PJ-Verweij/LowCostHighPrecisionPositioning-GNSSreferencestation/CAD_model/Solarpanel/Solarpanel.Victron_20watt.Assembly.SLDASM

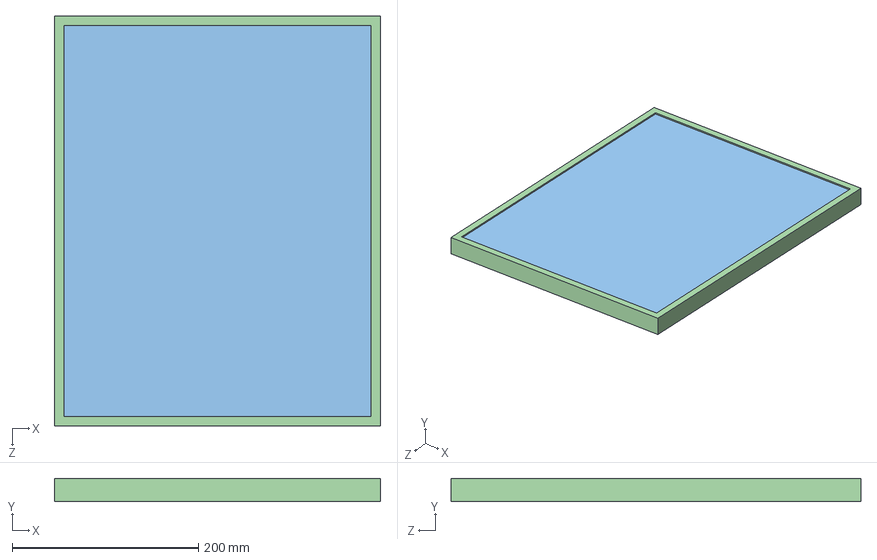
[picture p9: CAD file, 2021-05-01]
CAD_model/Solarpanel/Solarpanel.Victron_20watt.Assembly.SLDASM
350.0 x 25.0 x 440.0 mm
Solarpanel.sides
Solarpanel.glass
Solarpanel.cells
Solarpanel.backplate
