PJ-Verweij/LowCostHighPrecisionPositioning-GNSSreferencestation/CAD_model/Main_unit/PCB-components/Main-Unit.SIM800_GPRSmodem_Withheader.Assembly.SLDASM

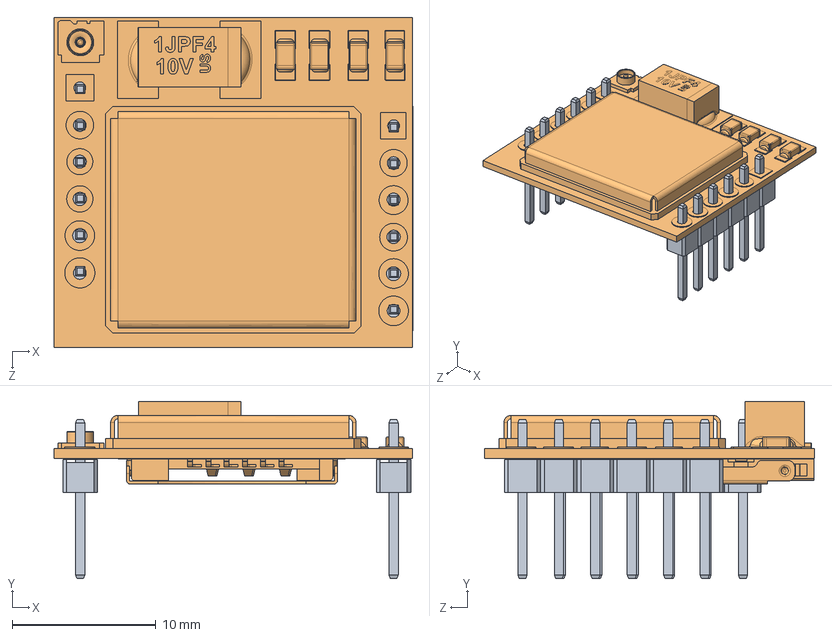
[picture p16: CAD file, 2021-05-01]
CAD_model/Main_unit/PCB-components/Main-Unit.SIM800_GPRSmodem_Withheader.Assembly.SLDASM
25.0 x 12.4 x 23.0 mm
Main-Unit.SIM800_GPRSmodem
Main-Unit.Male_Pin_2.54_mm x 12
