PJ-Verweij/LowCostHighPrecisionPositioning-GNSSreferencestation/CAD_model/Main_unit/Enclosure-components/Main-Unit.Enclosure.Box.SLDPRT

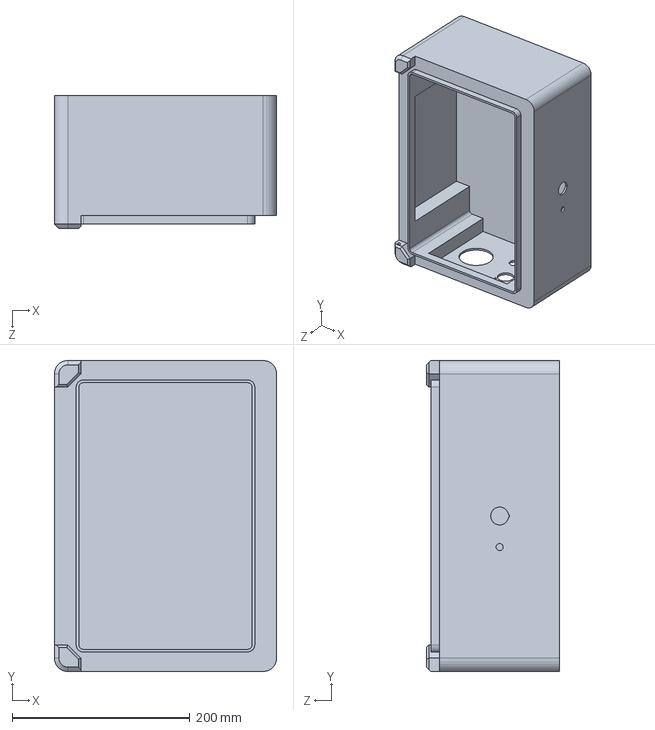
[picture p18: CAD file, 2021-05-01]
CAD_model/Main_unit/Enclosure-components/Main-Unit.Enclosure.Box.SLDPRT
250.0 x 350.0 x 150.0 mm
