PJ-Verweij/LowCostHighPrecisionPositioning-GNSSreferencestation/CAD_model/Main_unit/PCB-components/Main-Unit.Raspberry_PI_Zero.Assembly.SLDASM

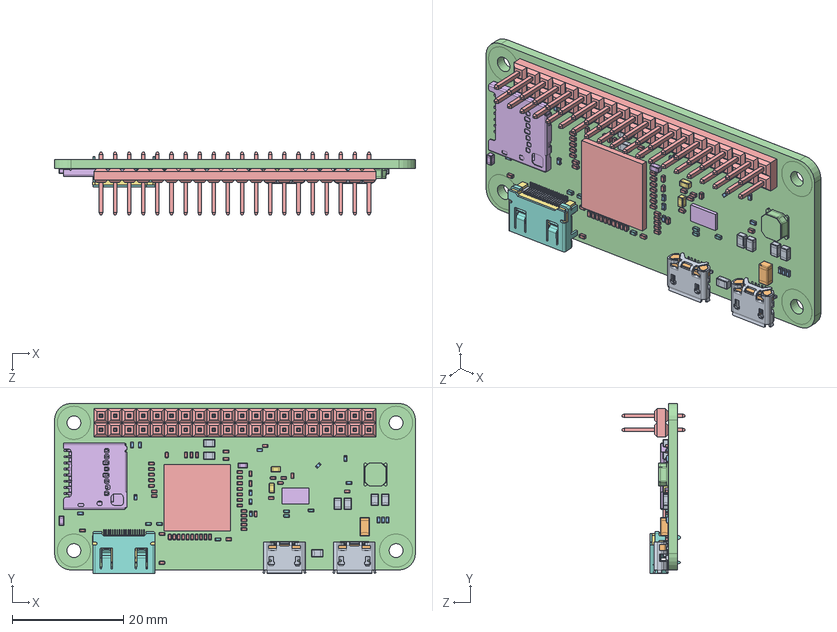
[picture p19: CAD file, 2021-05-01]
CAD_model/Main_unit/PCB-components/Main-Unit.Raspberry_PI_Zero.Assembly.SLDASM
65.0 x 30.6 x 11.4 mm
shield.step x 2
socket_housing.step x 2
socket_plate.step x 2
terminal.step x 10
CAPC-0402-T0.55-BN.step x 49
CAPC-0603-T0.9-BN.step x 2
INDC-0603.step x 2
INDC-0402.step x 6
CAPC-0805-T0.95-BN.step x 7
CAPC-1206-T1.4-BN.step
RESC-0402.step x 14
SRN4018.step
Components-0.step
Components-1.step
Housing.step
Shielding.step
Housing2.step
Pin1.step x 18
Pin2.step
Board.step
HDRV40W64P254_2X20_5080X508X838B.step
Micro SD slot.step
