PJ-Verweij/LowCostHighPrecisionPositioning-GNSSreferencestation/CAD_model/Main_unit/PCB-components/Pinheaders/Main-Unit.8x_Pinheader_2.54mm.Assembly.SLDASM

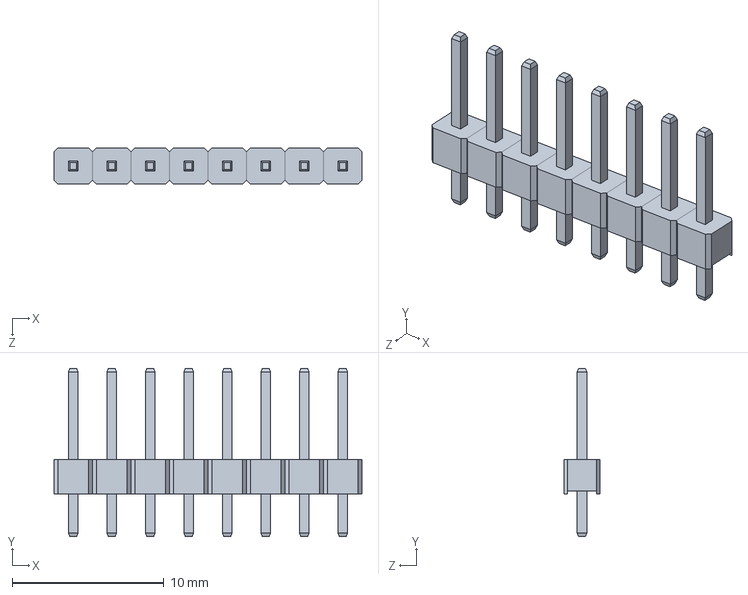
[picture p20: CAD file, 2021-05-01]
CAD_model/Main_unit/PCB-components/Pinheaders/Main-Unit.8x_Pinheader_2.54mm.Assembly.SLDASM
20.3 x 11.1 x 2.40 mm
Main-Unit.Male_Pin_2.54_mm x 8
