PJ-Verweij/LowCostHighPrecisionPositioning-GNSSreferencestation/CAD_model/Main_unit/Cable-gland-pg7-pg19/Main-Unit.Cable_Gland_PG9.Assembly.SLDASM

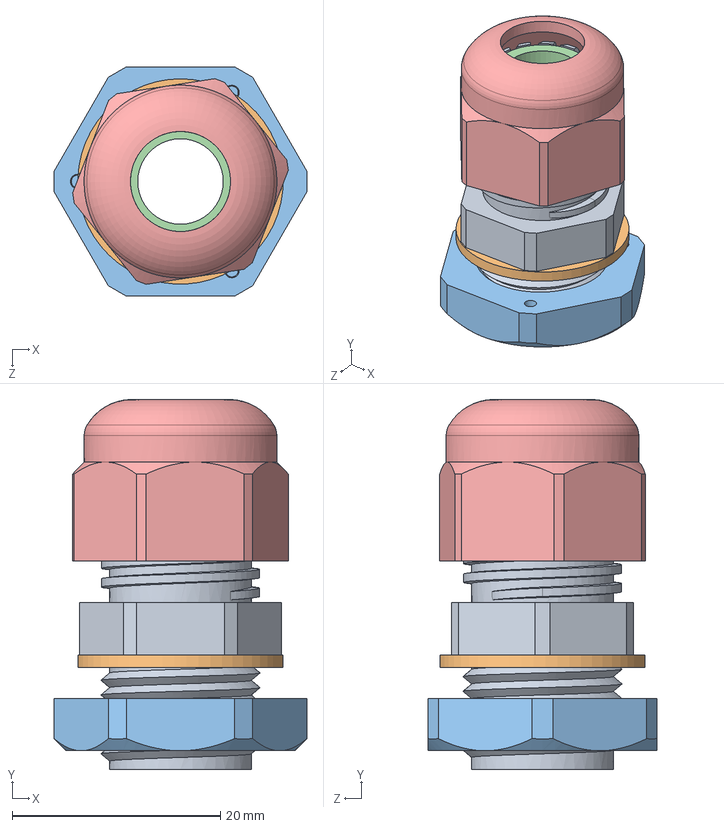
[picture p21: CAD file, 2021-05-01]
CAD_model/Main_unit/Cable-gland-pg7-pg19/Main-Unit.Cable_Gland_PG9.Assembly.SLDASM
24.2 x 35.5 x 22.0 mm
Cable Gland PG7-PG19 Body
Cable Gland PG7-PG19 Washer
Cable Gland PG7-PG19 Lock Nut
Cable Gland PG7-PG19 Sleeve
Cable Gland PG7-PG19 Gland Nut
