PJ-Verweij/LowCostHighPrecisionPositioning-GNSSreferencestation/CAD_model/Main_unit/Enclosure-components/Main-Unit.Case_LED_CML_19010051.SLDPRT

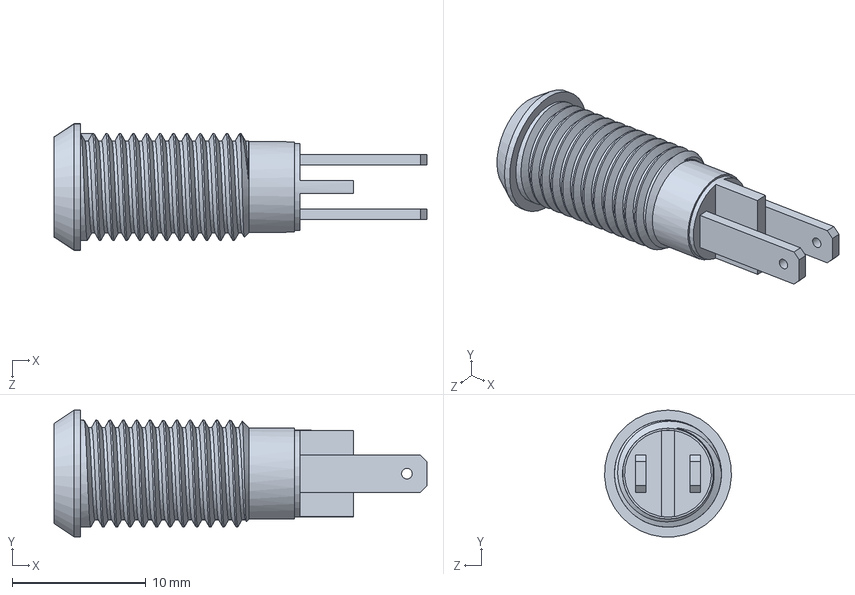
[picture p22: CAD file, 2021-05-01]
CAD_model/Main_unit/Enclosure-components/Main-Unit.Case_LED_CML_19010051.SLDPRT
27.9 x 9.48 x 9.49 mm
