PJ-Verweij/LowCostHighPrecisionPositioning-GNSSreferencestation/CAD_model/Main_unit/Enclosure-components/Main-Unit.Enclosure.Rubber.SLDPRT

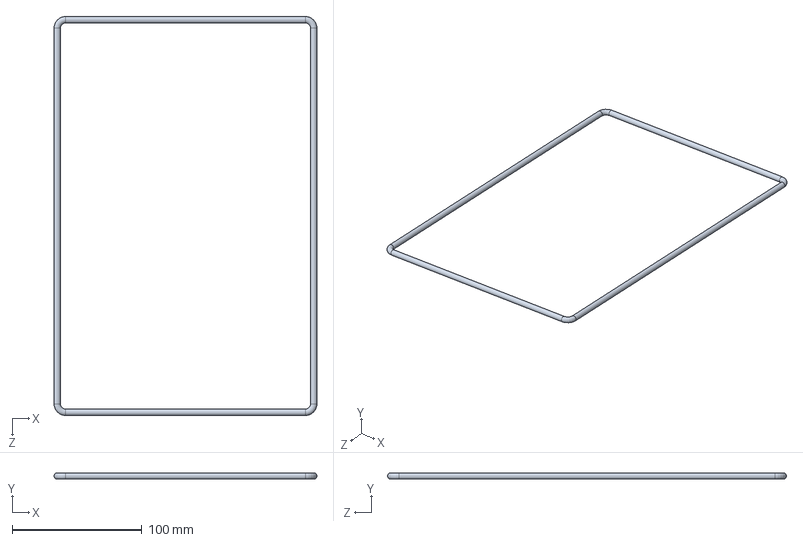
[picture p23: CAD file, 2021-05-01]
CAD_model/Main_unit/Enclosure-components/Main-Unit.Enclosure.Rubber.SLDPRT
203.0 x 5.00 x 308.0 mm
