PJ-Verweij/LowCostHighPrecisionPositioning-GNSSreferencestation/CAD_model/Main_unit/PCB-components/Main-Unit.M4_Insulated_crimp_ring.SLDPRT

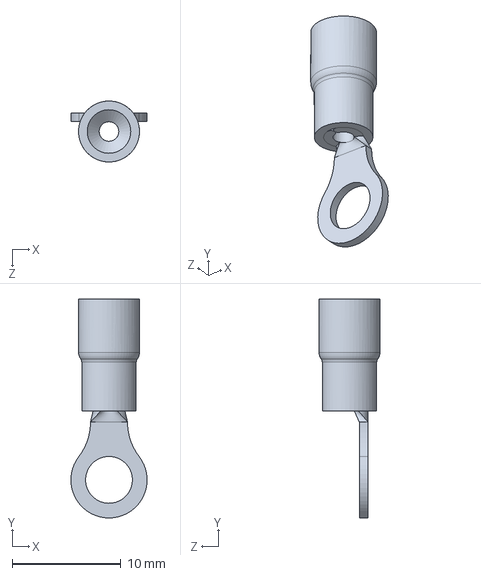
[picture p24: CAD file, 2021-05-01]
CAD_model/Main_unit/PCB-components/Main-Unit.M4_Insulated_crimp_ring.SLDPRT
7.00 x 20.1 x 5.60 mm
