PJ-Verweij/LowCostHighPrecisionPositioning-GNSSreferencestation/CAD_model/Antenna/Antenna.Antennatop.Assembly.SLDASM

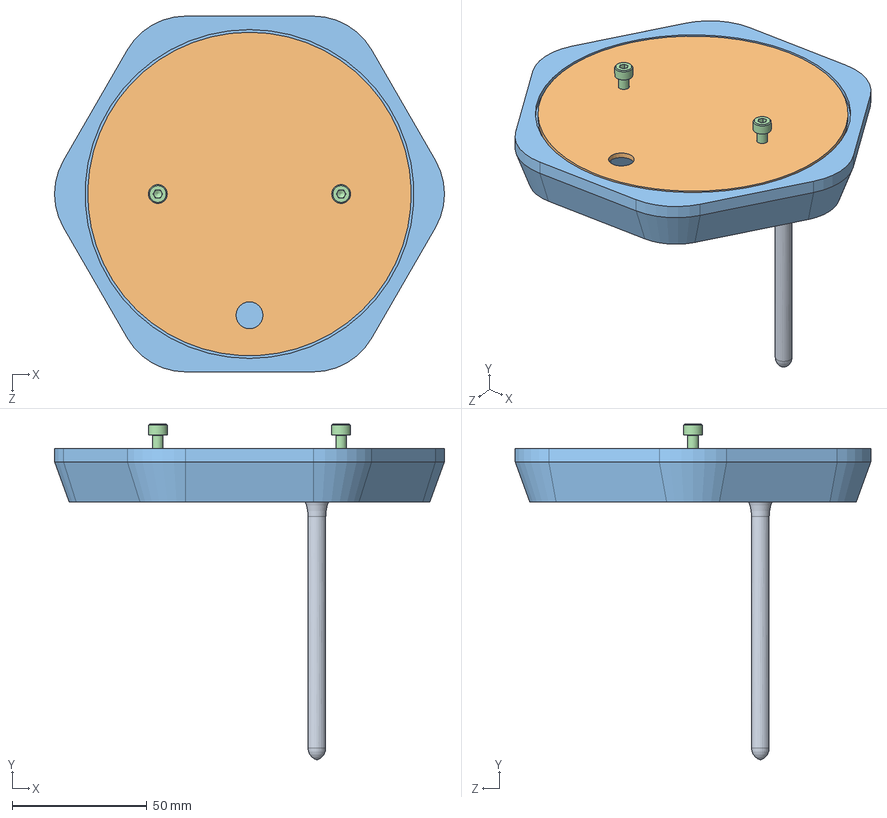
[picture p25: CAD file, 2021-05-01]
CAD_model/Antenna/Antenna.Antennatop.Assembly.SLDASM
144.7 x 124.6 x 132.0 mm
Antennatop.Base
Antennatop.Groundplane
Antennatop.Cellular-Antenna
socket head cap screw_am x 3
hex nut style 1_am x 2
