PJ-Verweij/LowCostHighPrecisionPositioning-GNSSreferencestation/CAD_model/Main_unit/PCB-components/Main-Unit.M2.5x10_hexagonal_spacer.SLDPRT

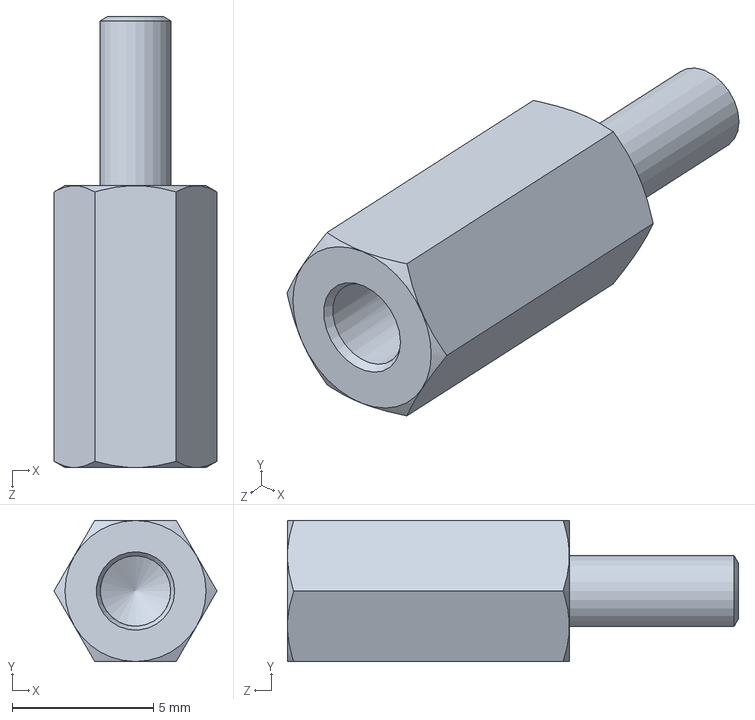
[picture p26: CAD file, 2021-05-01]
CAD_model/Main_unit/PCB-components/Main-Unit.M2.5x10_hexagonal_spacer.SLDPRT
5.78 x 5.01 x 16.0 mm
