PJ-Verweij/LowCostHighPrecisionPositioning-GNSSreferencestation/CAD_model/Main_unit/PCB-components/Main-Unit.SMA_Male_connector.SLDPRT

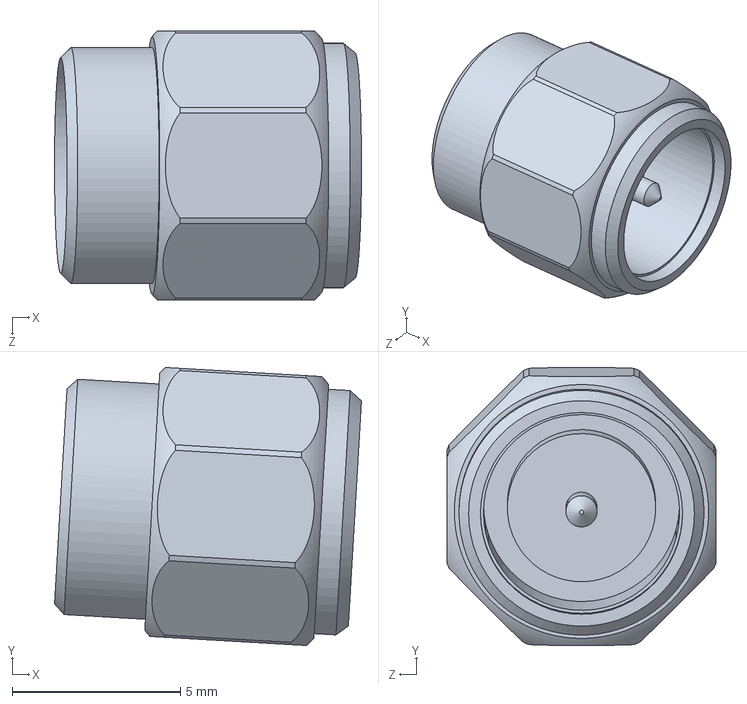
[picture p27: CAD file, 2021-05-01]
CAD_model/Main_unit/PCB-components/Main-Unit.SMA_Male_connector.SLDPRT
9.12 x 8.26 x 8.00 mm
