PJ-Verweij/LowCostHighPrecisionPositioning-GNSSreferencestation/CAD_model/Main_unit/Enclosure-components/Main-Unit.M4x10_Hexagonal_Spacer.SLDPRT

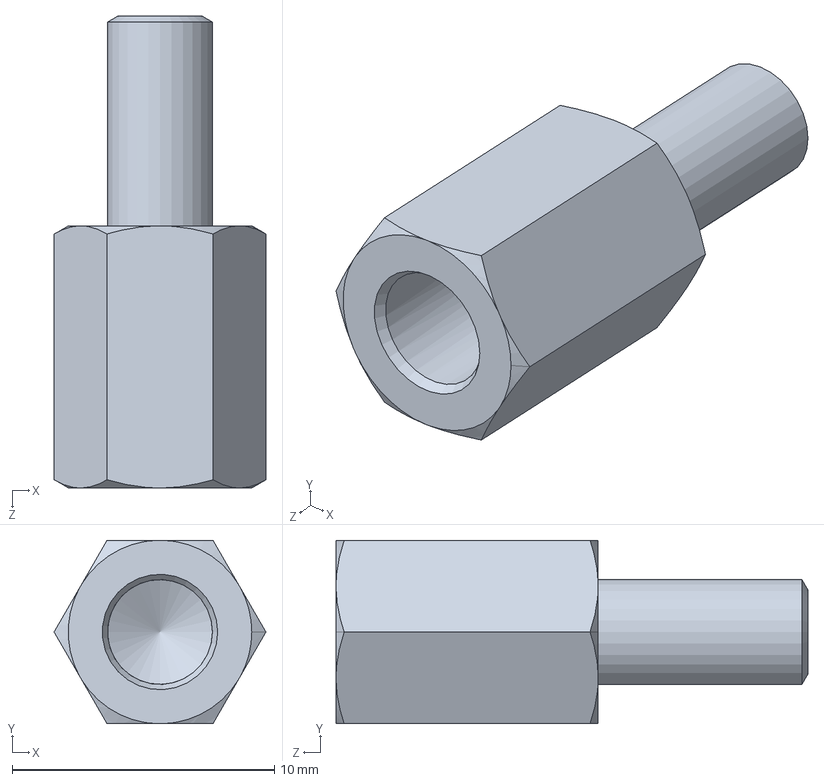
[picture p28: CAD file, 2021-05-01]
CAD_model/Main_unit/Enclosure-components/Main-Unit.M4x10_Hexagonal_Spacer.SLDPRT
8.08 x 7.00 x 18.0 mm
