PJ-Verweij/LowCostHighPrecisionPositioning-GNSSreferencestation/CAD_model/Main_unit/PCB-components/Main-Unit.5x20_Fuse.SLDPRT

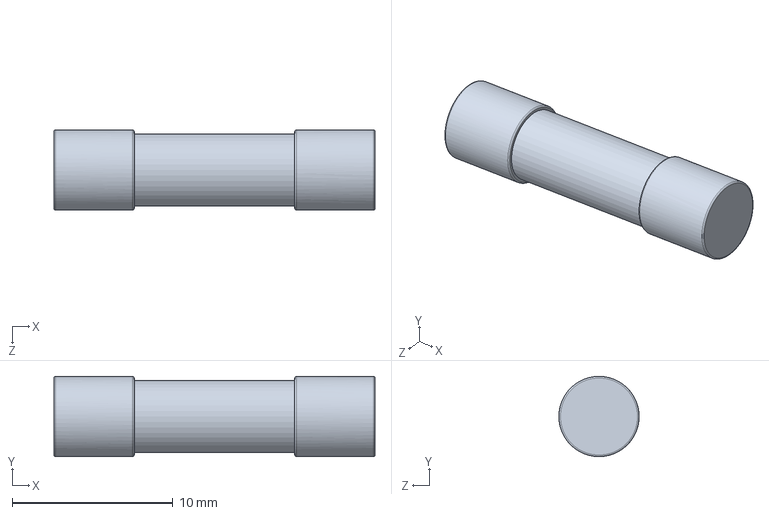
[picture p29: CAD file, 2021-05-01]
CAD_model/Main_unit/PCB-components/Main-Unit.5x20_Fuse.SLDPRT
20.0 x 5.00 x 5.00 mm
