PJ-Verweij/LowCostHighPrecisionPositioning-GNSSreferencestation/CAD_model/Antenna/Antennatop.Cellular-Antenna.SLDPRT

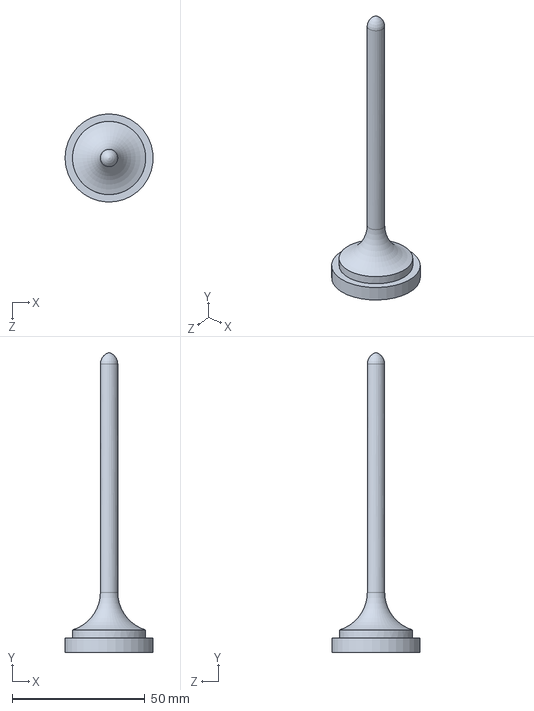
[picture p30: CAD file, 2021-05-01]
CAD_model/Antenna/Antennatop.Cellular-Antenna.SLDPRT
33.1 x 113.0 x 33.2 mm
