PJ-Verweij/LowCostHighPrecisionPositioning-GNSSreferencestation/CAD_model/Solarpanel/frame.SLDPRT

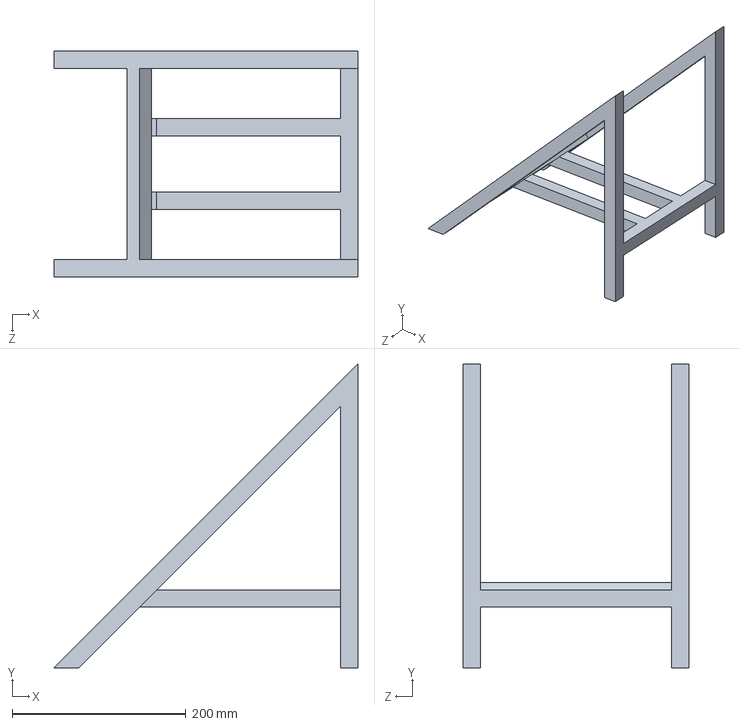
[picture p31: CAD file, 2021-05-01]
CAD_model/Solarpanel/frame.SLDPRT
350.0 x 350.0 x 260.0 mm
