PJ-Verweij/LowCostHighPrecisionPositioning-GNSSreferencestation/Productionfiles/Antennatop.Base-hole25,5mm.STL

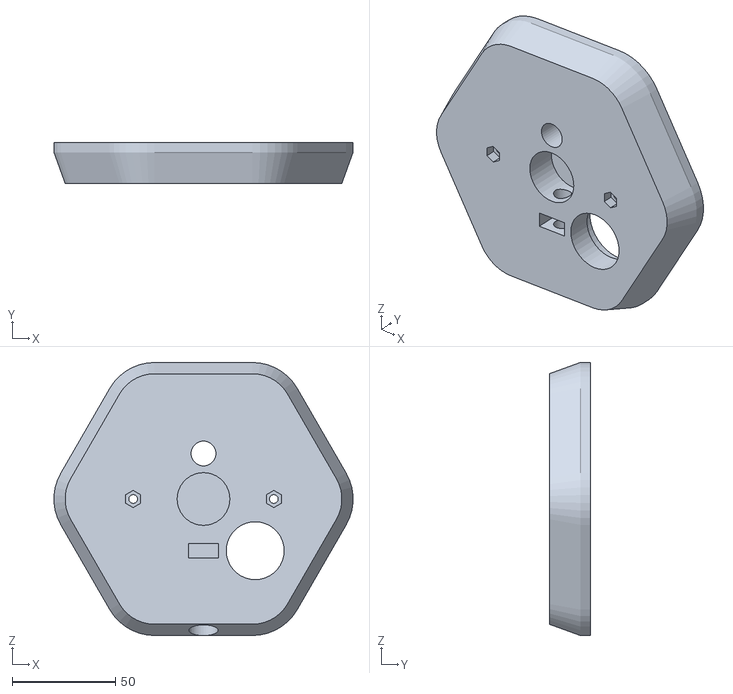
[picture p32: CAD file, 2021-05-01]
Productionfiles/Antennatop.Base-hole25,5mm.STL
144.5 x 20.0 x 132.0
