PJ-Verweij/LowCostHighPrecisionPositioning-GNSSreferencestation/CAD_model/Main_unit/Cable-gland-pg7-pg19/Cable Gland PG7-PG19 Sleeve.SLDPRT

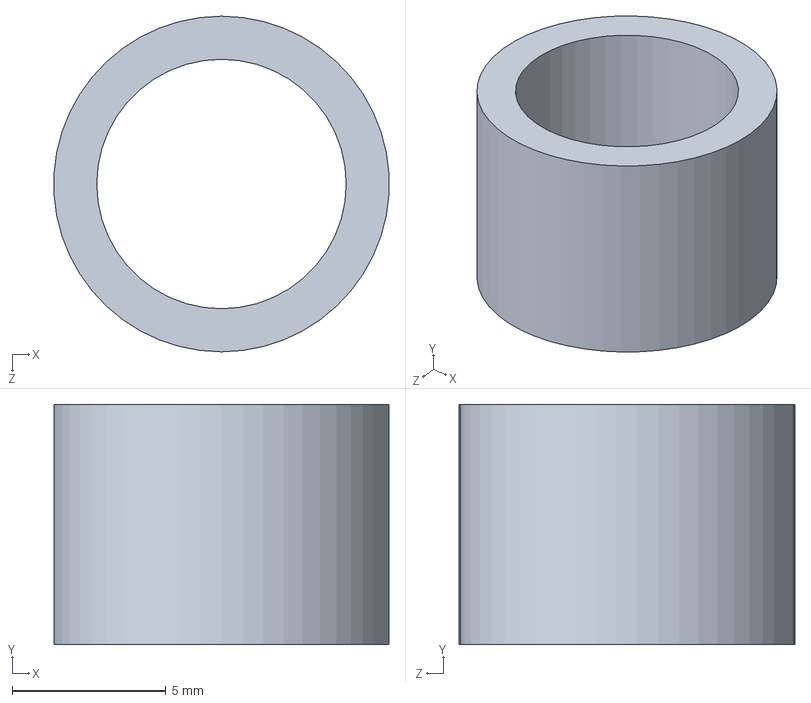
[picture p33: CAD file, 2021-05-01]
CAD_model/Main_unit/Cable-gland-pg7-pg19/Cable Gland PG7-PG19 Sleeve.SLDPRT
10.9 x 7.80 x 10.9 mm
