PJ-Verweij/LowCostHighPrecisionPositioning-GNSSreferencestation/CAD_model/Antenna/Antenna.Pole-1000mmx25mm.SLDPRT

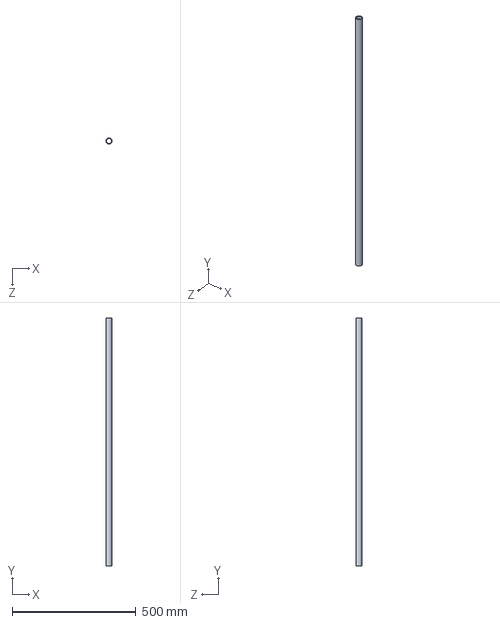
[picture p34: CAD file, 2021-05-01]
CAD_model/Antenna/Antenna.Pole-1000mmx25mm.SLDPRT
25.0 x 1000.0 x 25.0 mm
