PJ-Verweij/LowCostHighPrecisionPositioning-GNSSreferencestation/CAD_model/Main_unit/Toolbox-components/cross ph tapping 968_din.sldprt

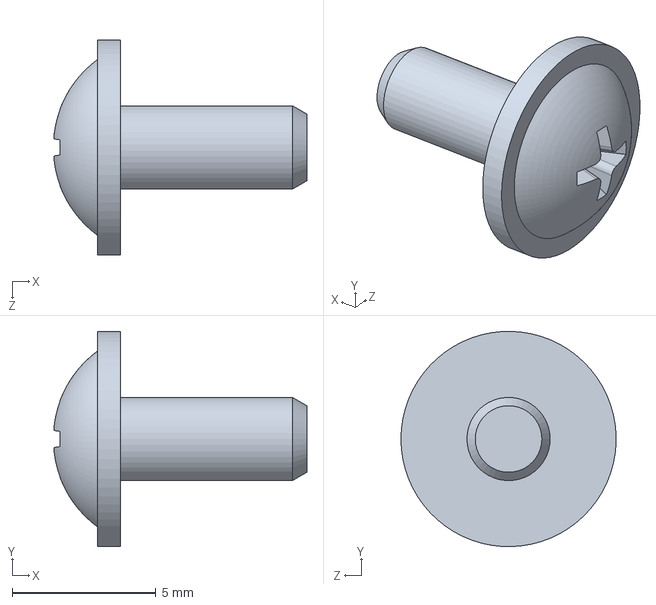
[picture p35: CAD file, 2021-05-01]
CAD_model/Main_unit/Toolbox-components/cross ph tapping 968_din.sldprt
8.81 x 7.50 x 7.50 mm
