PJ-Verweij/LowCostHighPrecisionPositioning-GNSSreferencestation/CAD_model/Solarpanel/Solarpanel.glass.SLDPRT

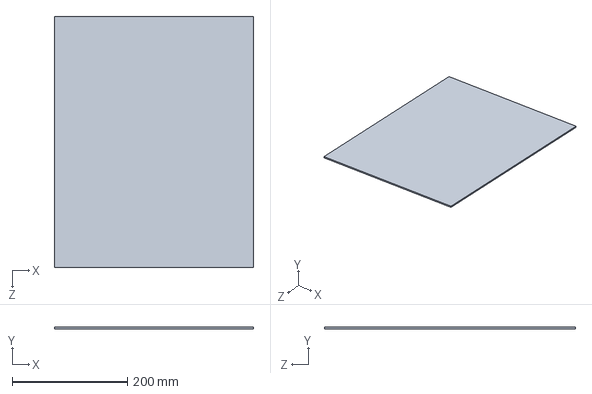
[picture p36: CAD file, 2021-05-01]
CAD_model/Solarpanel/Solarpanel.glass.SLDPRT
346.0 x 3.00 x 436.0 mm
