PJ-Verweij/LowCostHighPrecisionPositioning-GNSSreferencestation/CAD_model/Antenna/thread adapter antenna top.SLDPRT

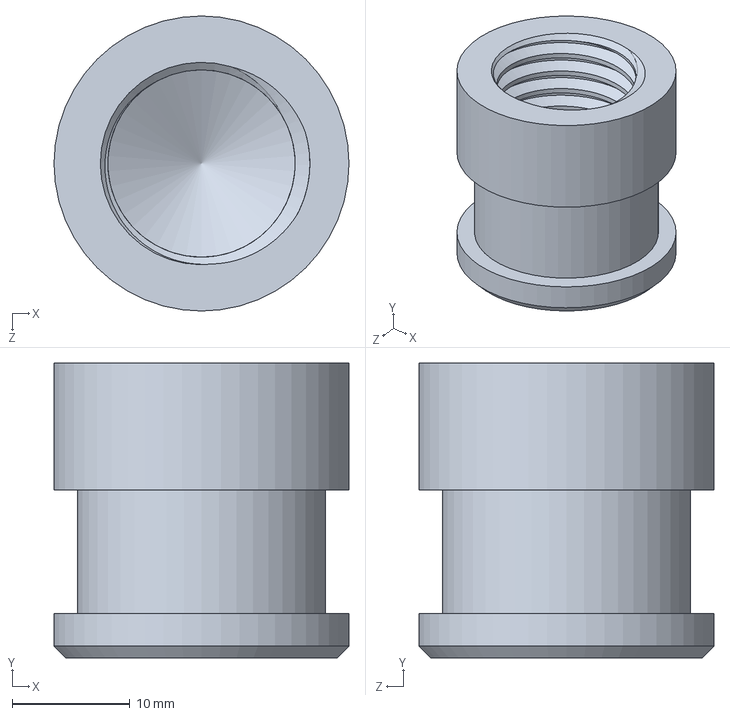
[picture p37: CAD file, 2021-05-01]
CAD_model/Antenna/thread adapter antenna top.SLDPRT
25.0 x 25.0 x 25.0 mm
