PJ-Verweij/LowCostHighPrecisionPositioning-GNSSreferencestation/CAD_model/Main_unit/Cable-gland-pg7-pg19/Cable Gland PG7-PG19 Body.SLDPRT

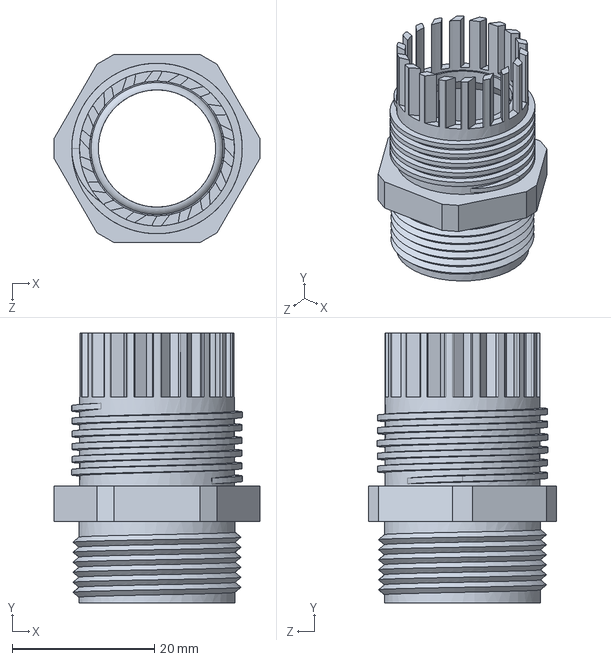
[picture p38: CAD file, 2021-05-01]
CAD_model/Main_unit/Cable-gland-pg7-pg19/Cable Gland PG7-PG19 Body.SLDPRT
29.0 x 38.0 x 26.5 mm
