PJ-Verweij/LowCostHighPrecisionPositioning-GNSSreferencestation/CAD_model/Solarpanel/Solarpanel.sides.SLDPRT

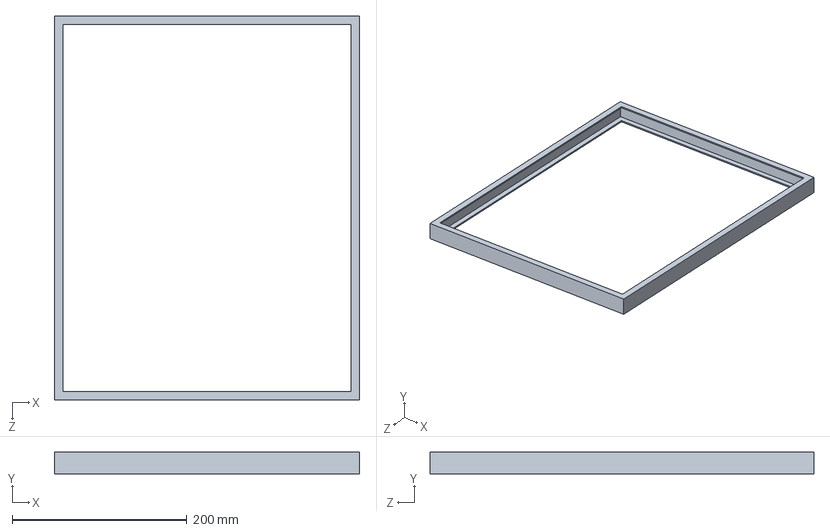
[picture p39: CAD file, 2021-05-01]
CAD_model/Solarpanel/Solarpanel.sides.SLDPRT
350.0 x 25.0 x 440.0 mm
