PJ-Verweij/LowCostHighPrecisionPositioning-GNSSreferencestation/CAD_model/Antenna/Antennatop.Groundplane.SLDPRT

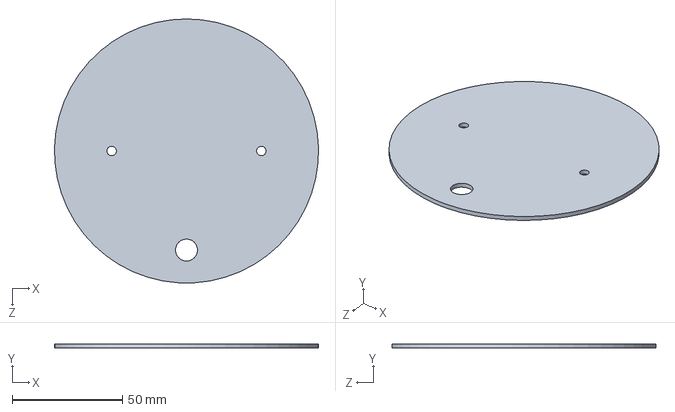
[picture p40: CAD file, 2021-05-01]
CAD_model/Antenna/Antennatop.Groundplane.SLDPRT
119.9 x 2.00 x 120.0 mm
