PJ-Verweij/LowCostHighPrecisionPositioning-GNSSreferencestation/CAD_model/Solarpanel/Solarpanel.cells.SLDPRT

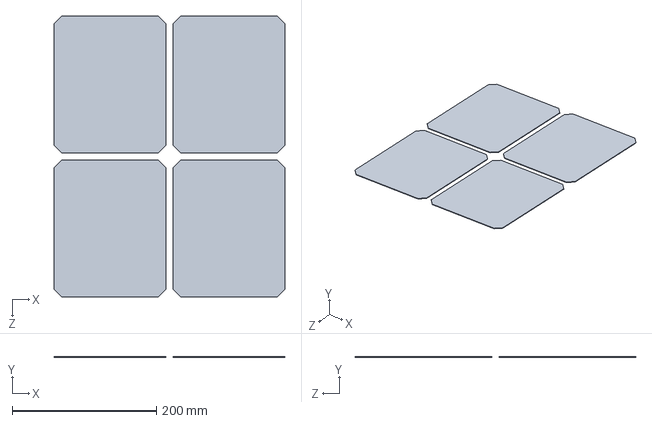
[picture p41: CAD file, 2021-05-01]
CAD_model/Solarpanel/Solarpanel.cells.SLDPRT
320.0 x 1.00 x 390.0 mm
