PJ-Verweij/LowCostHighPrecisionPositioning-GNSSreferencestation/CAD_model/Solarpanel/Solarpanel.Example-bracket.SLDPRT

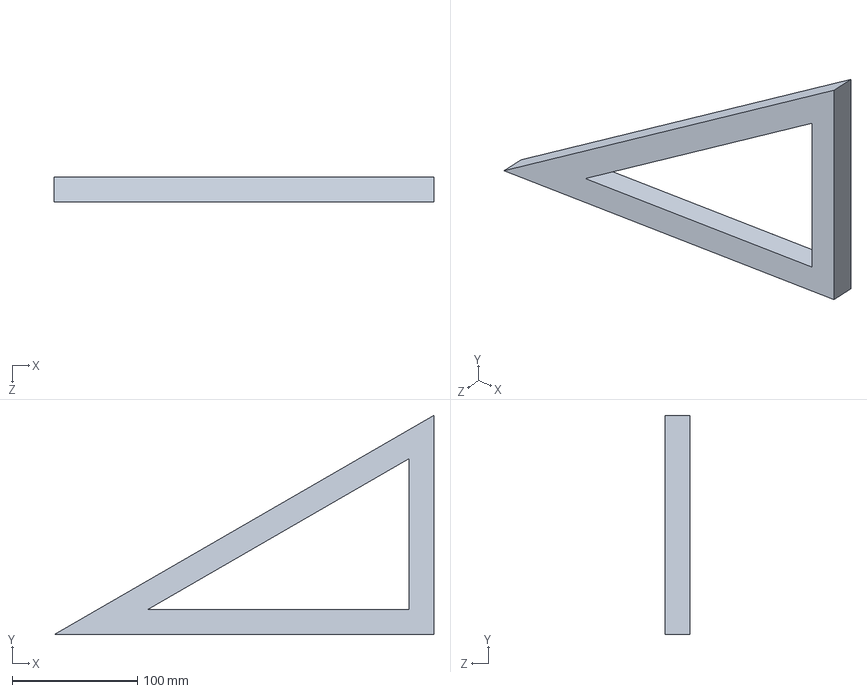
[picture p42: CAD file, 2021-05-01]
CAD_model/Solarpanel/Solarpanel.Example-bracket.SLDPRT
303.1 x 175.0 x 20.0 mm
