PJ-Verweij/LowCostHighPrecisionPositioning-GNSSreferencestation/CAD_model/Main_unit/PCB-components/Main-Unit.Example_Xbee.Assembly.sldasm

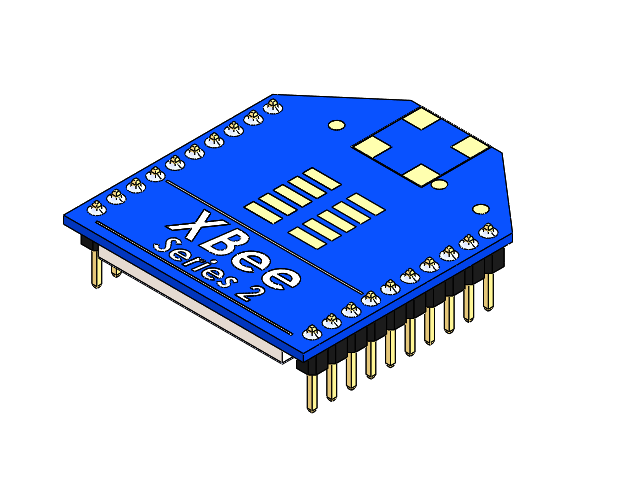
[picture p43: CAD file, 2021-05-01]
CAD_model/Main_unit/PCB-components/Main-Unit.Example_Xbee.Assembly.sldasm
Main-Unit.10x_Pinheader_2mm x 2
Main-Unit.Xbee_PCB
